TG-Techie/TG-Watch02-PCB/recalcitrant/TG-Watch02A-Flex-v2.brd

## EAGLE design recalcitrant/TG-Watch02A-Flex-v2.brd (2020-09-21)

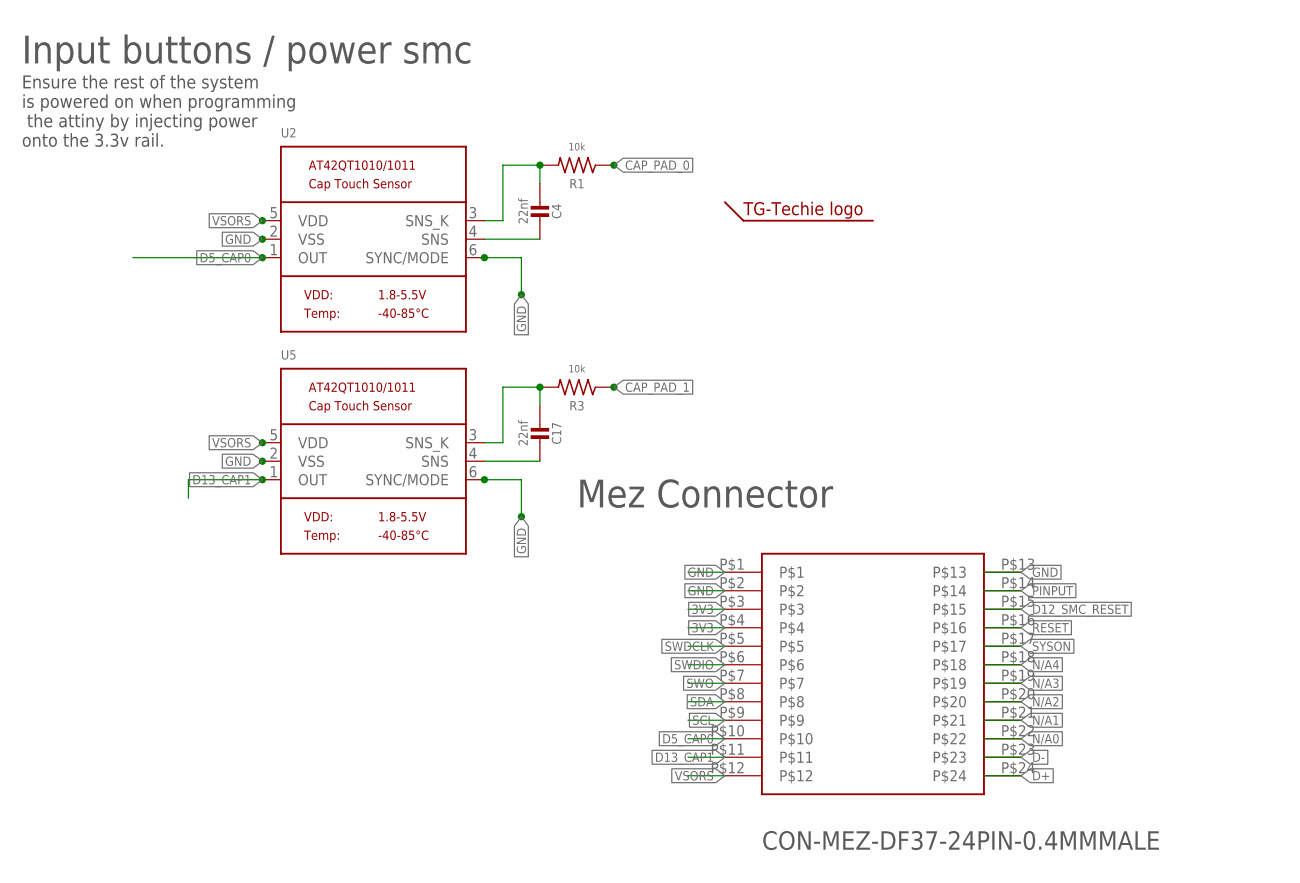
[picture p15: schematic TG-Watch02A-Flex-v2.sch]

Parts:
C4, C17: 22nf; _0402
R1, R3: 10k; TG_0402
U2, U5: SEN-CAPTOUCH-AT42QT1010/1; MICROBUILDER_SOT23-6
U$1: LOGO-TG-TECHIE2.5MM-SYMB; TG-LOGO-2.5MM-SYMB
U$11: CON-MEZ-DF37-24PIN-0.4MMMALE; MEZ-DF37B-24DP

Connections:
3V3: U$11.P$3, U$11.P$4
CAP_PAD_0: R1.1
CAP_PAD_1: R3.1
D5_CAP0: U2.1 (OUT), U$11.P$10
D12_SMC_RESET: U$11.P$15
D13_CAP1: U5.1 (OUT), U$11.P$11
D+: U$11.P$24
D-: U$11.P$23
GND: U2.2 (VSS), U2.6 (SYNC/MODE), U5.2 (VSS), U5.6 (SYNC/MODE), U$11.P$1, U$11.P$2, U$11.P$13
unnamed: C4.1, U2.4 (SNS)
unnamed: C4.2, R1.2, U2.3 (SNS_K)
unnamed: C17.1, U5.4 (SNS)
unnamed: C17.2, R3.2, U5.3 (SNS_K)
N/A0: U$11.P$22
N/A1: U$11.P$21
N/A2: U$11.P$20
N/A3: U$11.P$19
N/A4: U$11.P$18
PINPUT: U$11.P$14
RESET: U$11.P$16
SCL: U$11.P$9
SDA: U$11.P$8
SWDCLK: U$11.P$5
SWDIO: U$11.P$6
SWO: U$11.P$7
SYSON: U$11.P$17
VSORS: U2.5 (VDD), U5.5 (VDD), U$11.P$12

Notes on the sheet:
Input buttons / power smc
Ensure the rest of the system is powered on when programming the attiny by injecting power onto the 3.3v rail.
Mez Connector

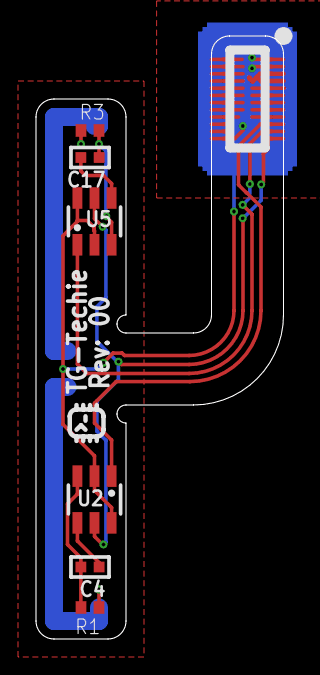
[picture p16: board TG-Watch02A-Flex-v2.brd from above]

Board: 2 copper layers, 13.8 x 33.5 mm, 8 parts (0 on the bottom side), 9 nets.
