TG-Techie/TG-Watch02-PCB/bat-brd-rev02-panel.brd

## EAGLE design bat-brd-rev02-panel.brd (2021-03-03)

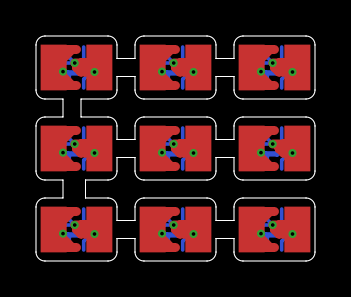
[picture p17: board bat-brd-rev02-panel.brd from above]

Board: 2 copper layers, 15.5 x 12.5 mm, 18 parts (0 on the bottom side), 18 nets.

Parts:
HEDR1, HEDR2, HEDR3, HEDR4, HEDR5, HEDR6, HEDR7, HEDR8, HEDR9: 1X02SMD; 1X2_SMD
U$1, U$2, U$3, U$4, U$5, U$6, U$7, U$8, U$9: CON-BAT-TG-MEZ_MALE; MEZ-DF37C-10DP

Connections:
GND: HEDR1.2, U$1.P$4, U$1.P$5, U$1.P$9, U$1.P$10
GND1: HEDR2.2, U$2.P$4, U$2.P$5, U$2.P$9, U$2.P$10
GND2: HEDR3.2, U$3.P$4, U$3.P$5, U$3.P$9, U$3.P$10
GND3: HEDR4.2, U$4.P$4, U$4.P$5, U$4.P$9, U$4.P$10
GND4: HEDR5.2, U$5.P$4, U$5.P$5, U$5.P$9, U$5.P$10
GND5: HEDR6.2, U$6.P$4, U$6.P$5, U$6.P$9, U$6.P$10
GND6: HEDR7.2, U$7.P$4, U$7.P$5, U$7.P$9, U$7.P$10
GND7: HEDR8.2, U$8.P$4, U$8.P$5, U$8.P$9, U$8.P$10
GND8: HEDR9.2, U$9.P$4, U$9.P$5, U$9.P$9, U$9.P$10
VBAT: HEDR1.1, U$1.P$1, U$1.P$2, U$1.P$6, U$1.P$7
VBAT1: HEDR2.1, U$2.P$1, U$2.P$2, U$2.P$6, U$2.P$7
VBAT2: HEDR3.1, U$3.P$1, U$3.P$2, U$3.P$6, U$3.P$7
VBAT3: HEDR4.1, U$4.P$1, U$4.P$2, U$4.P$6, U$4.P$7
VBAT4: HEDR5.1, U$5.P$1, U$5.P$2, U$5.P$6, U$5.P$7
VBAT5: HEDR6.1, U$6.P$1, U$6.P$2, U$6.P$6, U$6.P$7
VBAT6: HEDR7.1, U$7.P$1, U$7.P$2, U$7.P$6, U$7.P$7
VBAT7: HEDR8.1, U$8.P$1, U$8.P$2, U$8.P$6, U$8.P$7
VBAT8: HEDR9.1, U$9.P$1, U$9.P$2, U$9.P$6, U$9.P$7
